CelliesProjects/osap/src/presets.hpp

#pragma once

#include <Arduino.h>

struct source
{
    const char *name;
    const char *url;
};

constexpr struct source preset[]{

#ifdef USE_PRIVATE_PRESETS
#include "generated/private_presets.inc"
#endif

    {"NPO Radio1", "http://icecast.omroep.nl/radio1-bb-mp3"},
    {"NPO Radio2", "http://icecast.omroep.nl/radio2-bb-mp3"},
    {"NPO 3FM", "http://icecast.omroep.nl/3fm-bb-mp3"},
    {"NPO Klassiek", "http://icecast.omroep.nl/radio4-bb-mp3"},
    {"NPO Radio5", "http://icecast.omroep.nl/radio5-bb-mp3"},
    {"Radio Gelderland", "http://d2od87akyl46nm.cloudfront.net/icecast/omroepgelderland/radiogelderland"},
    {"DELTA RADIO NIJMEGEN", "http://streamdelta.lokaalradio.nl:9005/download.mp3"},
    {"Olympia Classics", "http://streams.olympia-streams.nl/classics192"},
    {"XXL Stenders", "http://streams.robstenders.nl:8063/bonanza_mp3"},
    {"192 Radio Nederland", "http://192radio.stream-server.nl/stream"},
    {"80s Hitradio Amsterdam", "http://s22.myradiostream.com:7728/"},
    {"Grolloo Radio", "https://de4.streamingpulse.com/ssl/7053"},
    {"Amsterdam Funk Channel", "https://stream.afc.fm/"},
    {"Jazz Radio Soul Food", "http://jazz-wr12.ice.infomaniak.ch/jazz-wr12-128.mp3"},
    {"Disco Mix", "https://play.discomix.ro/8002/stream"},
    {"Absoluut FM", "http://stream.laut.fm/absoluutfm"},
    {"Record DiscoFunk", "https://radiorecord.hostingradio.ru/discofunk96.aacp"},
    {"RadioEins", "http://radioeins.de/stream"},
    {"Planet 90", "https://planet90.beheerstream.nl/8010/stream"},
    {"Tekno1", "http://cressida.shoutca.st:8591/stream/1/"},
    {"Techno Frequency Radio", "http://stream.laut.fm/technofrequencyradio"},
    {"Hits 1 Algerie", "https://radio12.pro-fhi.net/listen/whmnrlow/stream"},
    {"bollywooddance", "https://nl4.mystreaming.net/uber/bollywooddance/icecast.audio"},
    {"bollywood", "http://2.mystreaming.net:80/er/bollywood/icecast.audio"},

};

constexpr const uint8_t NUMBER_OF_PRESETS = sizeof(preset) / sizeof(source);
